hkzlab/pontag/schematics_pcb/internal-pontag/4x1md_kicad_libraries/docs/images/3.5mm_6_contacts_4_conductors_audio_plug.png

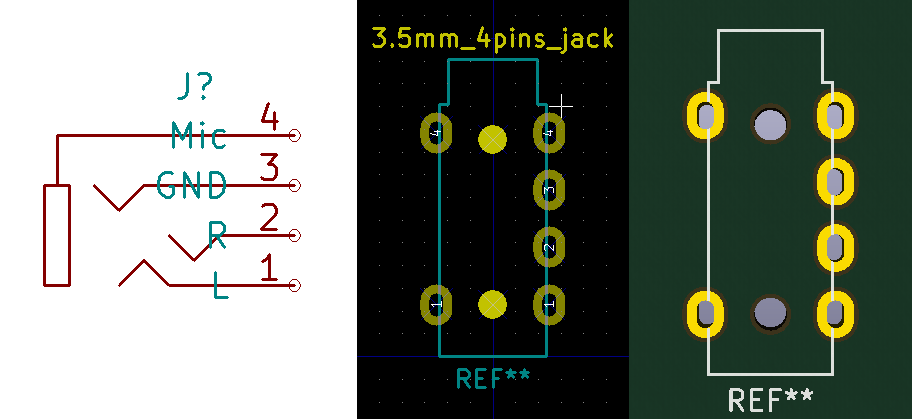
schematics_pcb/internal-pontag/4x1md_kicad_libraries/docs/images/3.5mm_6_contacts_4_conductors_audio_plug.png
