hkzlab/pontag/schematics_pcb/internal-pontag/4x1md_kicad_libraries/docs/images/Connector_MiniDIN_Female_6Pin_2rows_symbols.png

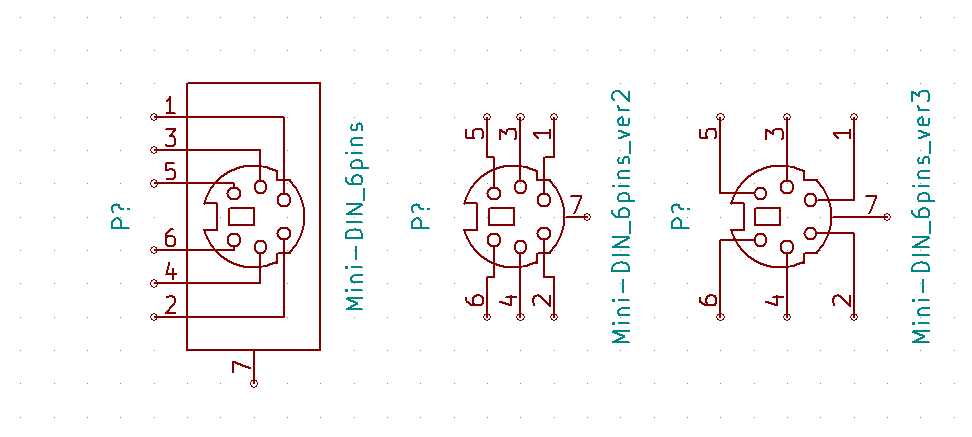
schematics_pcb/internal-pontag/4x1md_kicad_libraries/docs/images/Connector_MiniDIN_Female_6Pin_2rows_symbols.png
