hkzlab/pontag/schematics_pcb/internal-pontag/4x1md_kicad_libraries/docs/images/datasheets/Cliff_UT1x.png

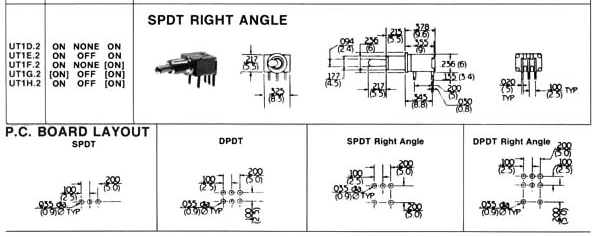
schematics_pcb/internal-pontag/4x1md_kicad_libraries/docs/images/datasheets/Cliff_UT1x.png
