hkzlab/pontag/schematics_pcb/internal-pontag/4x1md_kicad_libraries/docs/images/datasheets/Jack PJ-31060.jpg

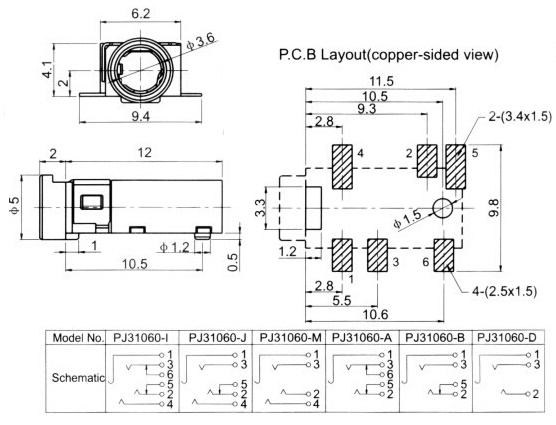
schematics_pcb/internal-pontag/4x1md_kicad_libraries/docs/images/datasheets/Jack PJ-31060.jpg
