hkzlab/pontag/schematics_pcb/internal-pontag/4x1md_kicad_libraries/docs/images/datasheets/Philmore_30-20001_SPDT_Switch.png

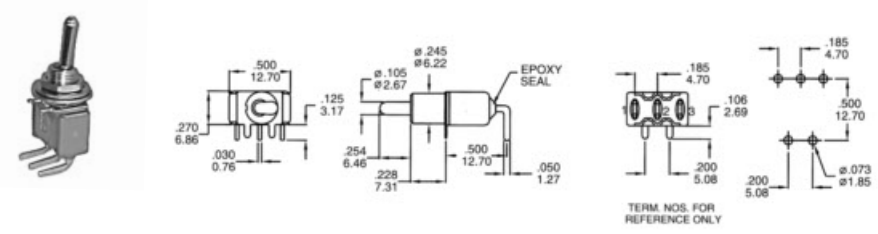
schematics_pcb/internal-pontag/4x1md_kicad_libraries/docs/images/datasheets/Philmore_30-20001_SPDT_Switch.png
