hkzlab/pontag/schematics_pcb/internal-pontag/4x1md_kicad_libraries/docs/images/datasheets/PJ-320DS.png

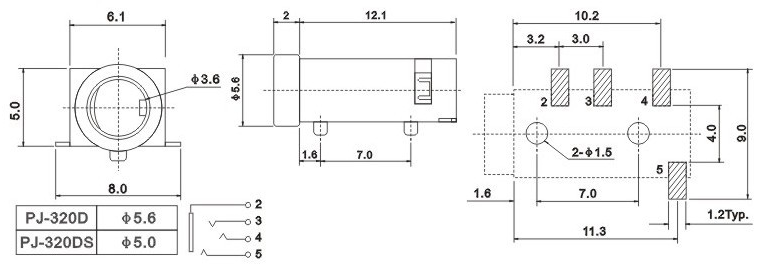
schematics_pcb/internal-pontag/4x1md_kicad_libraries/docs/images/datasheets/PJ-320DS.png
