hkzlab/pontag/schematics_pcb/internal-pontag/4x1md_kicad_libraries/docs/images/datasheets/PJ-320E.png

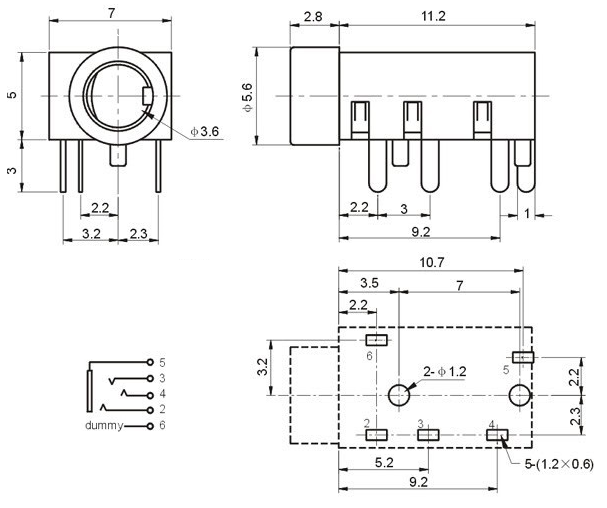
schematics_pcb/internal-pontag/4x1md_kicad_libraries/docs/images/datasheets/PJ-320E.png
