hkzlab/pontag/schematics_pcb/internal-pontag/4x1md_kicad_libraries/docs/images/datasheets/Quectel_L80_GPS_Module_2.png

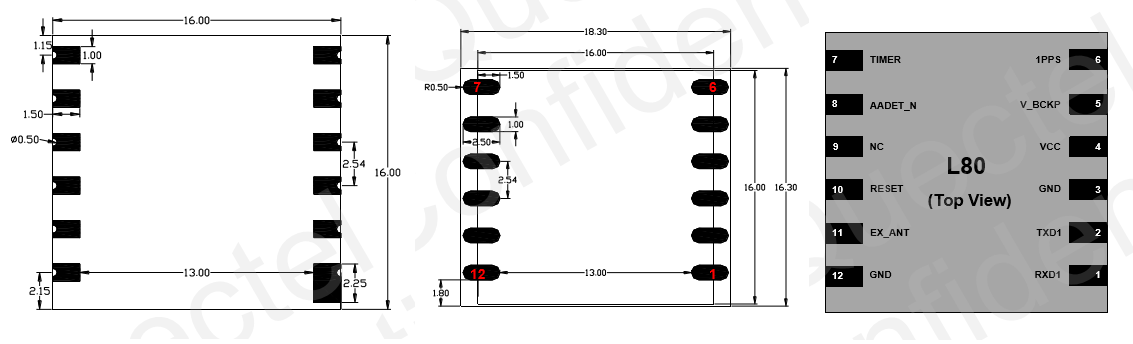
schematics_pcb/internal-pontag/4x1md_kicad_libraries/docs/images/datasheets/Quectel_L80_GPS_Module_2.png
