hkzlab/pontag/schematics_pcb/internal-pontag/4x1md_kicad_libraries/docs/images/datasheets/Seiko_MS621FE-FL11E_dia.png

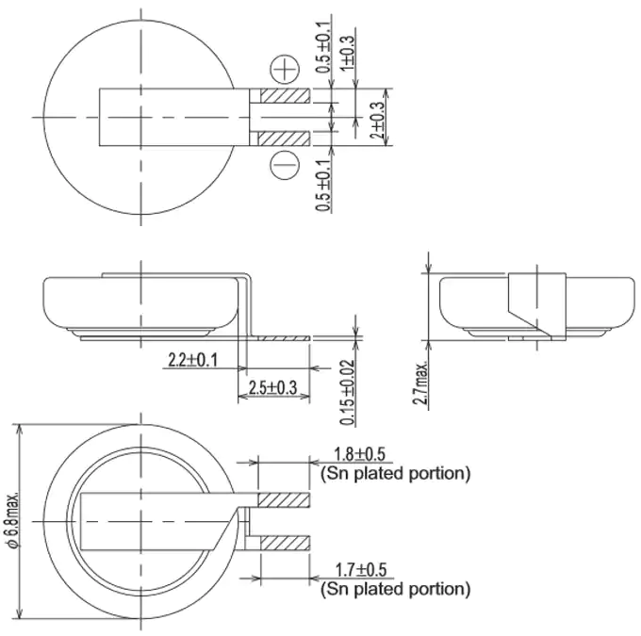
schematics_pcb/internal-pontag/4x1md_kicad_libraries/docs/images/datasheets/Seiko_MS621FE-FL11E_dia.png
