hkzlab/pontag/schematics_pcb/internal-pontag/4x1md_kicad_libraries/docs/images/datasheets/USB Micro 5 pin SMT B.jpg

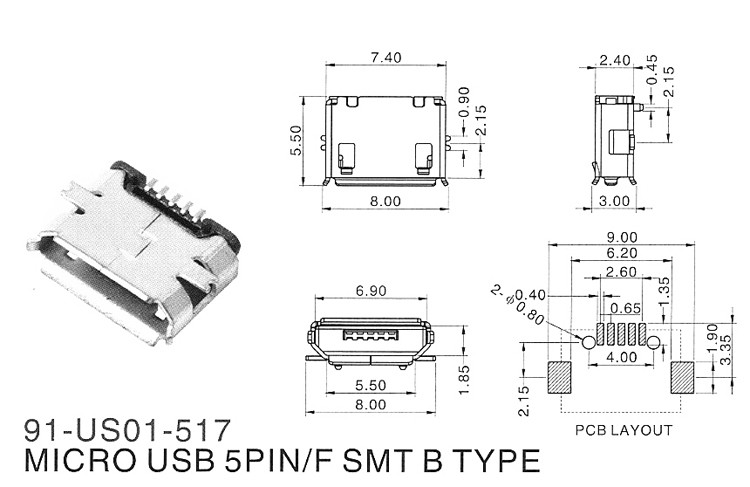
schematics_pcb/internal-pontag/4x1md_kicad_libraries/docs/images/datasheets/USB Micro 5 pin SMT B.jpg
