hkzlab/pontag/schematics_pcb/internal-pontag/4x1md_kicad_libraries/docs/images/datasheets/USB Micro 5pin Through hole.jpg

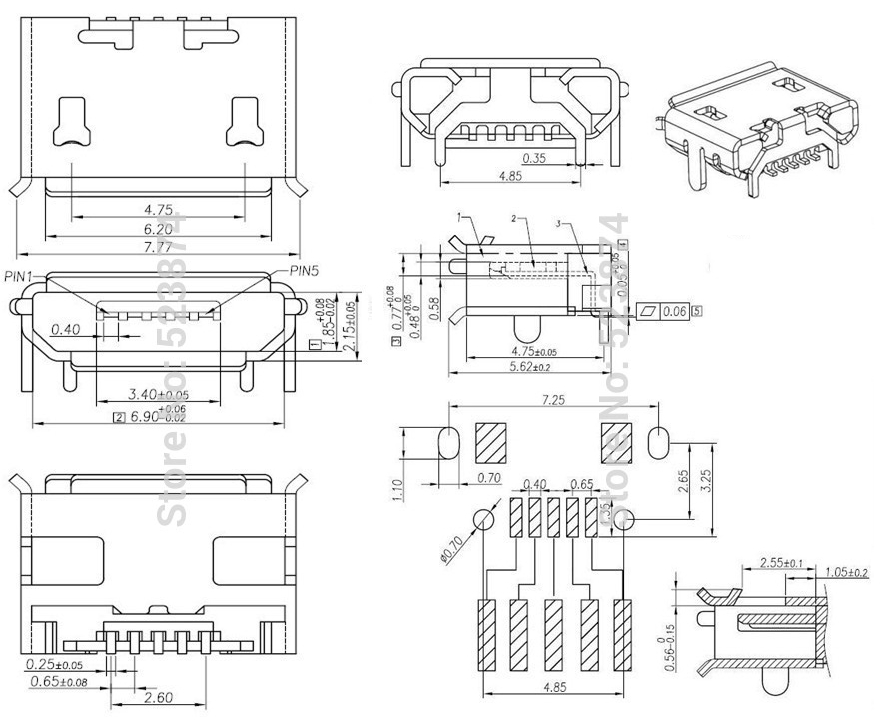
schematics_pcb/internal-pontag/4x1md_kicad_libraries/docs/images/datasheets/USB Micro 5pin Through hole.jpg
