hkzlab/pontag/schematics_pcb/internal-pontag/4x1md_kicad_libraries/docs/images/datasheets/USB_Mini_Horizontal.jpg

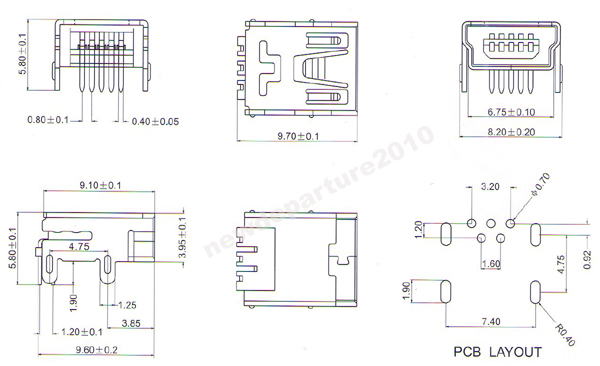
schematics_pcb/internal-pontag/4x1md_kicad_libraries/docs/images/datasheets/USB_Mini_Horizontal.jpg
