hkzlab/pontag/schematics_pcb/internal-pontag/4x1md_kicad_libraries/docs/images/Gms-g9_GNSS_Module.png

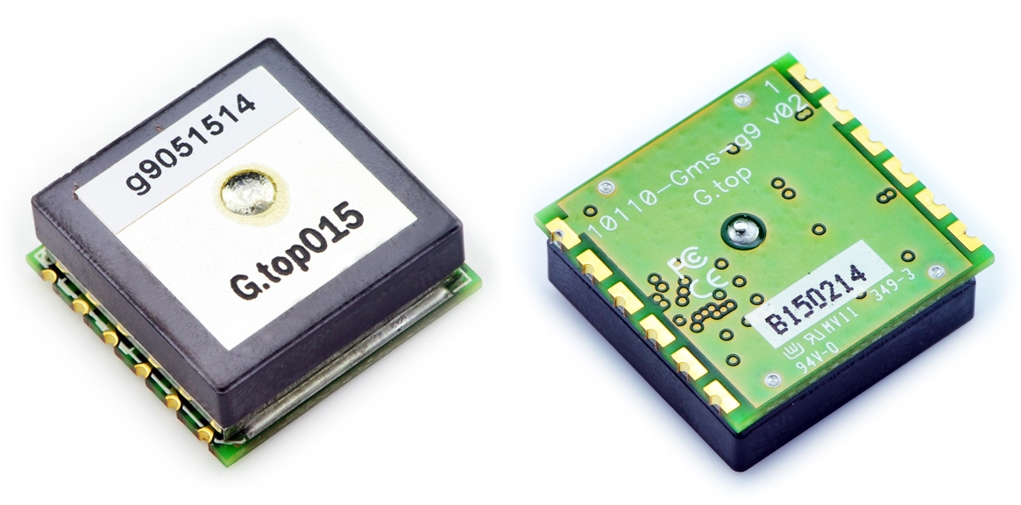
schematics_pcb/internal-pontag/4x1md_kicad_libraries/docs/images/Gms-g9_GNSS_Module.png
