hkzlab/pontag/schematics_pcb/internal-pontag/4x1md_kicad_libraries/docs/images/microampermeter.jpg

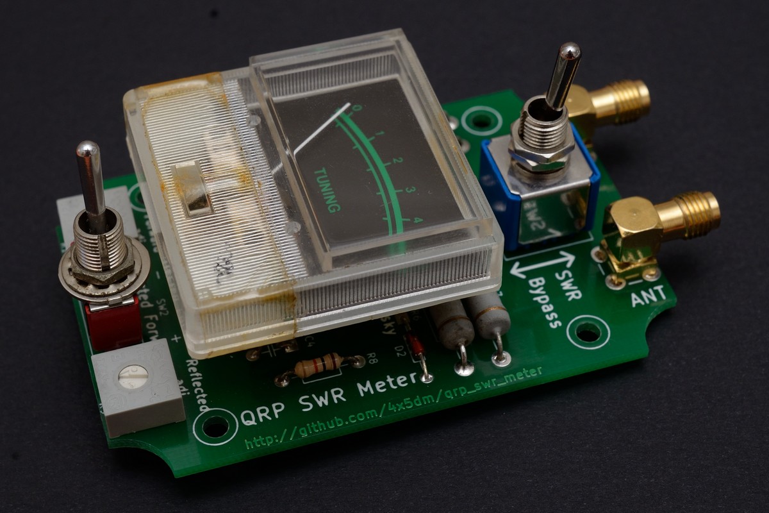
schematics_pcb/internal-pontag/4x1md_kicad_libraries/docs/images/microampermeter.jpg
