hkzlab/pontag/schematics_pcb/internal-pontag/4x1md_kicad_libraries/docs/images/microampermeter.png

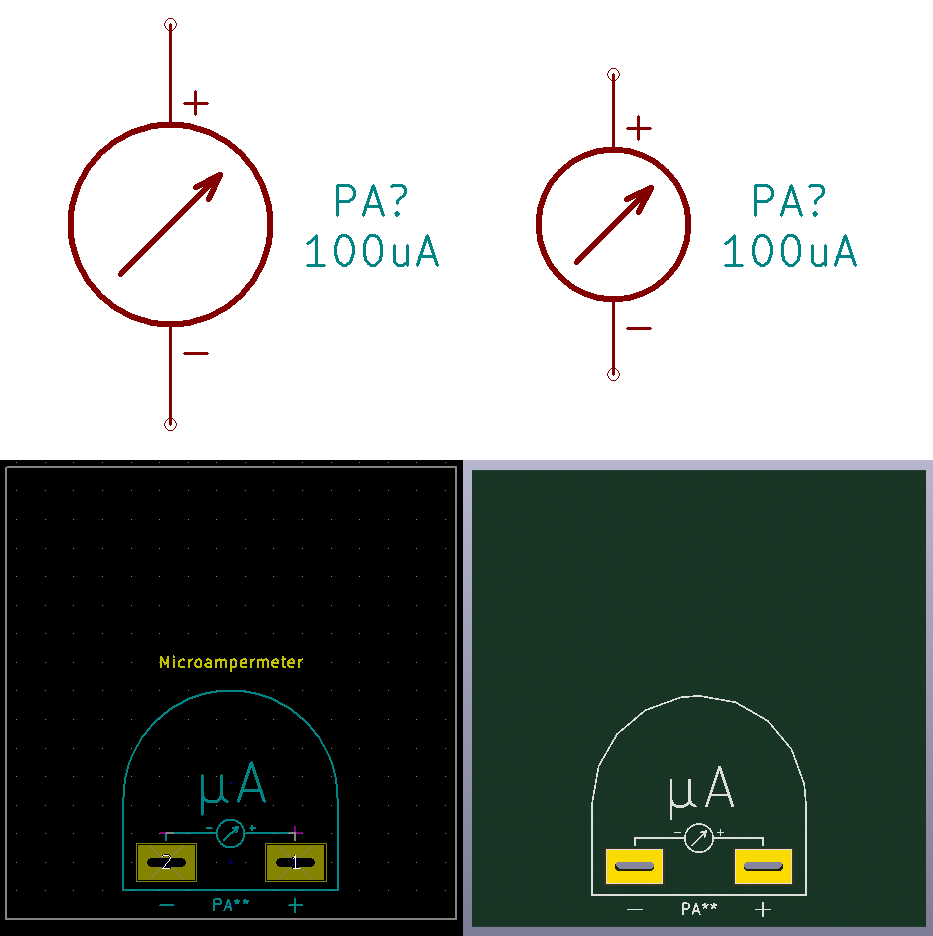
schematics_pcb/internal-pontag/4x1md_kicad_libraries/docs/images/microampermeter.png
