hkzlab/pontag/schematics_pcb/internal-pontag/4x1md_kicad_libraries/docs/images/mini_usb_throughhole.png

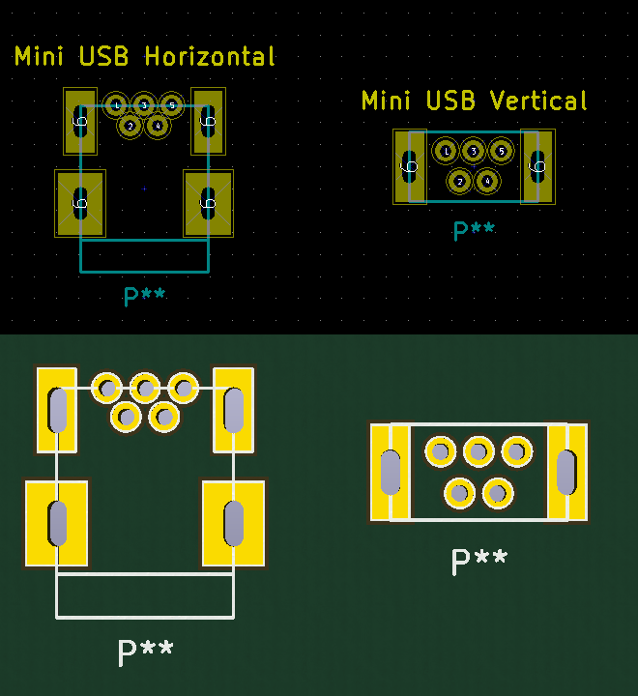
schematics_pcb/internal-pontag/4x1md_kicad_libraries/docs/images/mini_usb_throughhole.png
