hkzlab/pontag/schematics_pcb/internal-pontag/4x1md_kicad_libraries/docs/images/PJ-320DS.jpg

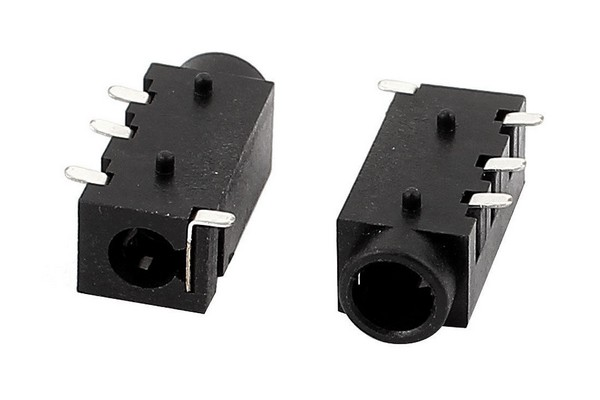
schematics_pcb/internal-pontag/4x1md_kicad_libraries/docs/images/PJ-320DS.jpg
