hkzlab/pontag/schematics_pcb/internal-pontag/4x1md_kicad_libraries/docs/images/PJ-31060.png

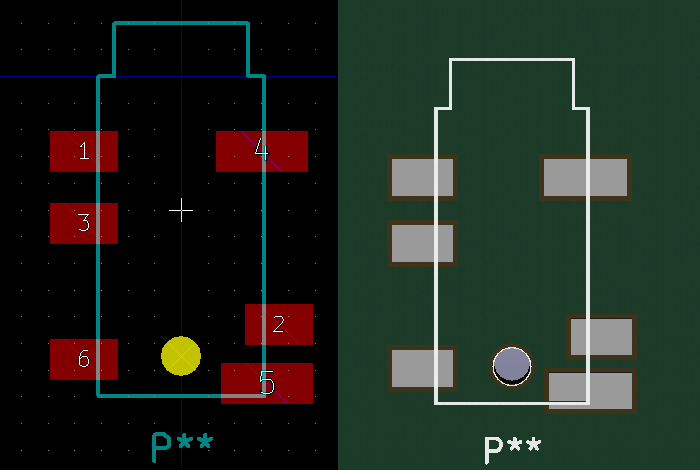
schematics_pcb/internal-pontag/4x1md_kicad_libraries/docs/images/PJ-31060.png
