hkzlab/pontag/schematics_pcb/internal-pontag/4x1md_kicad_libraries/docs/images/Quectel_L80_GPS_Module.jpg

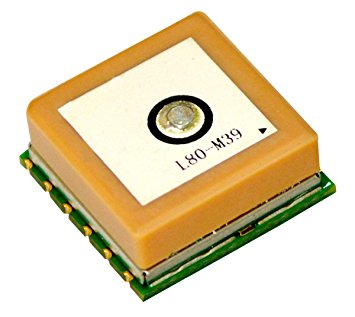
schematics_pcb/internal-pontag/4x1md_kicad_libraries/docs/images/Quectel_L80_GPS_Module.jpg
