hkzlab/pontag/schematics_pcb/internal-pontag/4x1md_kicad_libraries/docs/images/SPDT-slide-switch.png

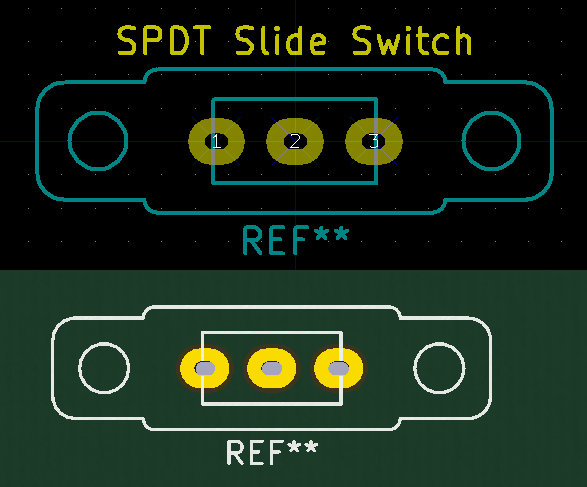
schematics_pcb/internal-pontag/4x1md_kicad_libraries/docs/images/SPDT-slide-switch.png
