hkzlab/pontag/schematics_pcb/internal-pontag/4x1md_kicad_libraries/docs/images/installation/symbols_2.png

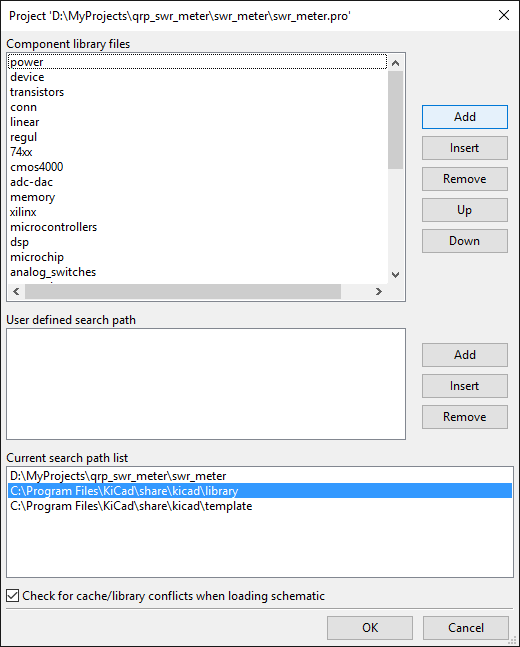
schematics_pcb/internal-pontag/4x1md_kicad_libraries/docs/images/installation/symbols_2.png
